dbhaig/Musical_Toy/enclosure/helix.scad

/* helix.scad
 *
 *    OpenSCAD script to generate a tubular helix
 *
 *    Adapted from https://github.com/KitWallace/openscad/blob/master/spring.scad 
 *
 */

$fn= 50;

//radius = radius of helix
//wire_r = radius of wire 
//pitch =  distance between coils
//coils =  number of coils
//step =   helix resolution - in degrees

module helix(radius = 100, wire_r = 1, pitch = 25, coils = 4, step = 5) {

function m_translate(v) = [ [1, 0, 0, 0],
                            [0, 1, 0, 0],
                            [0, 0, 1, 0],
                            [v.x, v.y, v.z, 1  ] ];
                            
function m_rotate(v) =  [ [1,  0,         0,        0],
                          [0,  cos(v.x),  sin(v.x), 0],
                          [0, -sin(v.x),  cos(v.x), 0],
                          [0,  0,         0,        1] ]
                      * [ [ cos(v.y), 0,  -sin(v.y), 0],
                          [0,         1,  0,        0],
                          [ sin(v.y), 0,  cos(v.y), 0],
                          [0,         0,  0,        1] ]
                      * [ [ cos(v.z),  sin(v.z), 0, 0],
                          [-sin(v.z),  cos(v.z), 0, 0],
                          [ 0,         0,        1, 0],
                          [ 0,         0,        0, 1] ];
                            
function vec3(v) = [v.x, v.y, v.z];

function transform(v, m)  = vec3([v.x, v.y, v.z, 1] * m);
                            
function orientate(p0, p) =               
              m_rotate([0, atan2(sqrt(pow(p[0], 2) + pow(p[1], 2)), p[2]), 0])  
            * m_rotate([0, 0, atan2(p[1], p[0])]) 
            * m_translate(p0);

function circle_points(r = 1, a = 0) = 
    a < 360
       ? concat([[r * sin(a),  r * cos(a),0]], circle_points(r, a + 360 / $fn)) 
       : [] ;

function loop_points(step, end , t = 0) = 
    t <= end 
       ? concat([f(t)], loop_points(step, end, t + step)) 
       : [] ;

function transform_points(list, matrix, i = 0) = 
    i < len(list) 
       ? concat([ transform(list[i], matrix) ], transform_points(list, matrix, i + 1))
       : [];

function tube_points(loop_points, section_points, i=0) =
    i < len(loop_points)-1
       ? concat(
           transform_points(
                 section_points, 
                 orientate(loop_points[i],(loop_points[i + 1]- loop_points[i])/2)),
          tube_points(loop_points,section_points, i + 1)
        )
       : []    // in a closed loop, this segment connects to the start
;

function tube_faces(facets, s, i = 0) =  
     i < facets  
       ?  concat([[s * facets + i, 
                   s * facets + (i + 1) % facets, 
                  (s + 1) * facets + (i + 1) % facets, 
                  (s + 1) * facets + i]
                ], 
                tube_faces(facets, s, i + 1))
      : [];
          
function tube_end(facets, s, i = 0) =  
     i < facets  
       ?  concat( [s * facets + i], tube_end(facets, s, i+1))
       : [];  
 
                                       
function loop_faces(segs,facets, j = 0) = 
     j < segs
        ? concat(tube_faces(facets,  j), loop_faces(segs, facets, j + 1)) 
        : [];

function loop_all_faces(segs,facets) =
     concat ([reverse(tube_end(facets,0))], // direction changed here 
              loop_faces(segs,facets),
             [tube_end(facets,segs)]
            );

function reverse_r(v,n) =
      n == 0 
        ? [v[0]]
        : concat([v[n]],reverse_r(v,n-1))
;
function reverse(v) = reverse_r(v, len(v)-1);


function circle_points(r = 1, a = 0) = 
    a < 360
       ? concat([[r * sin(a),  r * cos(a),0]], circle_points(r, a + 360 / $fn)) 
       : [] ;

function f(t) =  [radius *sin(t),radius * cos(t) ,pitch * t/360 ];

function loop_points(step, end, t = 0) = 
    t <= end 
       ? concat([f(t)], loop_points(step, end, t + step )) 
       : [] ;

section_points = circle_points(wire_r, 360/$fn);

loop_points = loop_points(step ,360* coils + step);

tube_points = tube_points(loop_points,section_points);

faces = loop_all_faces(len(loop_points)-2, len(section_points));

    color("yellow") polyhedron(points = tube_points, faces = faces, center=true);
}

//helix();
